WebmasterTD/CastVolumeKnob/esp8266/volume.py

import usocket as socket
import ussl as ssl
import ure as re
import utime as time
import machine
from neopixel import NeoPixel
from ustruct import unpack
import math
import wificonf
import esp
INIT_MSGS = (
            b'\x00\x00\x00Y\x08\x00\x12\x08sender-0\x1a\nreceiver-0"(urn:x-cast:com.google.cast.tp.connection(\x002\x13{"type": "CONNECT"}',
            b'\x00\x00\x00g\x08\x00\x12\x08sender-0\x1a\nreceiver-0"#urn:x-cast:com.google.cast.receiver(\x002&{"type": "GET_STATUS", "requestId": 1}'
            )

VOL_MSGS =  {
            4 : b'\x00\x00\x00\x81\x08\x00\x12\x08sender-0\x1a\nreceiver-0"#urn:x-cast:com.google.cast.receiver(\x002@{"type": "SET_VOLUME", "volume": {"level": ###}, "requestId": $$$}',
            5 : b'\x00\x00\x00\x82\x08\x00\x12\x08sender-0\x1a\nreceiver-0"#urn:x-cast:com.google.cast.receiver(\x002A{"type": "SET_VOLUME", "volume": {"level": ###}, "requestId": $$$}',
            6 : b'\x00\x00\x00\x83\x08\x00\x12\x08sender-0\x1a\nreceiver-0"#urn:x-cast:com.google.cast.receiver(\x002B{"type": "SET_VOLUME", "volume": {"level": ###}, "requestId": $$$}',
            7 : b'\x00\x00\x00\x84\x08\x00\x12\x08sender-0\x1a\nreceiver-0"#urn:x-cast:com.google.cast.receiver(\x002C{"type": "SET_VOLUME", "volume": {"level": ###}, "requestId": $$$}',
            8 : b'\x00\x00\x00\x85\x08\x00\x12\x08sender-0\x1a\nreceiver-0"#urn:x-cast:com.google.cast.receiver(\x002D{"type": "SET_VOLUME", "volume": {"level": ###}, "requestId": $$$}'
            }

STOP_MSGS = {
            1 : b'\x00\x00\x00\x96\x08\x00\x12\x08sender-0\x1a\nreceiver-0"#urn:x-cast:com.google.cast.receiver(\x002U{"type": "STOP", "requestId": $$$, "sessionId": "###"}',
            2 : b'\x00\x00\x00\x97\x08\x00\x12\x08sender-0\x1a\nreceiver-0"#urn:x-cast:com.google.cast.receiver(\x002V{"type": "STOP", "requestId": $$$, "sessionId": "###"}',
            3 : b'\x00\x00\x00\x98\x08\x00\x12\x08sender-0\x1a\nreceiver-0"#urn:x-cast:com.google.cast.receiver(\x002W{"type": "STOP", "requestId": $$$, "sessionId": "###"}'
            }

GAMMA8 =    (  
            0,  0,  0,  0,  0,  0,  0,  0,  0,  0,  0,  0,  0,  0,  0,  0,
            0,  0,  0,  0,  0,  0,  0,  0,  0,  0,  0,  0,  1,  1,  1,  1,
            1,  1,  1,  1,  1,  1,  1,  1,  1,  2,  2,  2,  2,  2,  2,  2,
            2,  3,  3,  3,  3,  3,  3,  3,  4,  4,  4,  4,  4,  5,  5,  5,
            5,  6,  6,  6,  6,  7,  7,  7,  7,  8,  8,  8,  9,  9,  9, 10,
            10, 10, 11, 11, 11, 12, 12, 13, 13, 13, 14, 14, 15, 15, 16, 16,
            17, 17, 18, 18, 19, 19, 20, 20, 21, 21, 22, 22, 23, 24, 24, 25,
            25, 26, 27, 27, 28, 29, 29, 30, 31, 32, 32, 33, 34, 35, 35, 36,
            37, 38, 39, 39, 40, 41, 42, 43, 44, 45, 46, 47, 48, 49, 50, 50,
            51, 52, 54, 55, 56, 57, 58, 59, 60, 61, 62, 63, 64, 66, 67, 68,
            69, 70, 72, 73, 74, 75, 77, 78, 79, 81, 82, 83, 85, 86, 87, 89,
            90, 92, 93, 95, 96, 98, 99,101,102,104,105,107,109,110,112,114,
            115,117,119,120,122,124,126,127,129,131,133,135,137,138,140,142,
            144,146,148,150,152,154,156,158,160,162,164,167,169,171,173,175,
            177,180,182,184,186,189,191,193,196,198,200,203,205,208,210,213,
            215,218,220,223,225,228,231,233,236,239,241,244,247,249,252,255
            )


class Chromecast(object):        
    
    def __init__(self, ip):
        self.ip = ip
        self.request = 2
        self.s = socket.socket(socket.AF_INET, socket.SOCK_STREAM)
        self.s.connect((self.ip, 8009))
        self.s = ssl.wrap_socket(self.s)
        for msg in INIT_MSGS:
            self.s.write(msg)
        self.read_message()
       
    @property
    def get_volume(self):
        return self.vol


    def set_volume(self, volume):
        volume = str(volume/100)
        msg_len = len(volume) + len(str(self.request))
        r_volmsg = VOL_MSGS[msg_len]
        r_volmsg = r_volmsg.replace(b'###', bytes(volume, 'utf-8'))
        r_volmsg = r_volmsg.replace(b'$$$', bytes(str(self.request), 'utf-8'))
        self.s.write(r_volmsg)
        self.request += 1
        self.read_message()

    def disconnect(self):
        self.s.close()
    
    def read_message(self):
        siz = unpack('>I',self.s.read(4))[0]
        status = str(self.s.read(siz))
        self.vol = float(re.search('\"level\":([0-9]\.?[0-9]*)', status).group(1))
        self.vol = int(round(self.vol*100))
        self.sess_id = re.search('\"sessionId\":\"(....................................)', status)
        if self.sess_id:
            self.sess_id = self.sess_id.group(1)
        
    
    def stop_playback(self):
        if self.sess_id:
            msg_size = len(str(self.request))
            stop_msg = STOP_MSGS[msg_size]
            stop_msg = stop_msg.replace(b'###', bytes(self.sess_id, 'utf-8'))
            stop_msg = stop_msg.replace(b'$$$', bytes(str(self.request), 'utf-8'))
            #print(stop_msg)
            self.s.write(stop_msg)
            self.request += 1
            self.read_message()

class NeoPixelRing(NeoPixel):
    
    def __init__(self, led_v_pin, device, *args, **kwargs):
        self.led_v = machine.Pin(led_v_pin, machine.Pin.OUT)
        self.colors = wificonf.DEVICE_COLORS
        self.lightness = wificonf.LED_LIGHTNESS
        self.device = device
        self.turn_on()
        super(NeoPixelRing, self).__init__(*args, **kwargs)

    def change_device(self, device, volume):
        vol = int(volume)
        self.device = device
        rev = list(enumerate(self.vol2pix(vol), 1))
        h, s, v = self.colors[self.device]
        for i in range(16):
            self[i] = self.hsv2rgb(h, s, v)
            self.write()
            time.sleep_ms(30)

        time.sleep_ms(100)
        
        for i, c in rev[::-1]:
            h, s, v = c
            self[i] = self.hsv2rgb(h, s, v)
            self.write()
            time.sleep_ms(30)
        

        self.set_vol(volume)

    def set_vol(self, volume):
        vol = int(volume)
        h, s, v = self.colors[self.device]
        self[0] = self.hsv2rgb(h, s, v)
        for i, color in enumerate(self.vol2pix(vol), 1):
            h, s, v = color
            self[i] = self.hsv2rgb(h, s, v)
        self.write()

    def vol2pix(self, volume):
        pixels = wificonf.neopixel_percents
        hues =   wificonf.neopixel_hues
        for h, p in zip(hues, pixels):
            if (volume/p) > 1:
                yield (h, 1, 1)
            elif (volume/p) > 0:
                yield (h, 1, volume/p)
            else:
                yield (h, 1, 0)
            volume = volume - p
        return

    def error(self):
        for _ in range(3):
            self.fill(self.hsv2rgb(30, 1, 1))
            self.write()
            time.sleep_ms(150)
            self.fill((0, 0, 0))
            self.write()
            time.sleep_ms(100)

    def stop(self):
        self.fill(self.hsv2rgb(0, 1, 1))
        self.write()

    def turn_off(self):
        self.fill((0, 0, 0))
        self.write()
        self.led_v.off()

    def turn_on(self):
        self.led_v.on()

    def hsv2rgb(self, h, s, v):
        h = float(h)
        s = float(s)
        v = float(v) * self.lightness
        h60 = h / 60.0
        h60f = math.floor(h60)
        hi = int(h60f) % 6
        f = h60 - h60f
        p = v * (1 - s)
        q = v * (1 - f * s)
        t = v * (1 - (1 - f) * s)
        r, g, b = 0, 0, 0
        if hi == 0: r, g, b = v, t, p
        elif hi == 1: r, g, b = q, v, p
        elif hi == 2: r, g, b = p, v, t
        elif hi == 3: r, g, b = p, q, v
        elif hi == 4: r, g, b = t, p, v
        elif hi == 5: r, g, b = v, p, q
        r, g, b = int(r * 255), int(g * 255), int(b * 255)
        return GAMMA8[r], GAMMA8[g], GAMMA8[b]
