WebmasterTD/CastVolumeKnob/esp8266/wificonf_example.py

WIFI_SSID = 'YOUR WIFI SSID'
WIFI_PASSWORD = 'YOUR WIFI PASSWORD'
#               IP address,         netmask,        gateway,        DNS
WIFI_CONFIG = ('192.168.0.150', '255.255.255.0', '192.168.0.1', '192.168.0.1')

#set chomecasts ips and names here in your network
CHROMECASTS  = {'192.168.0.164':'LG SH6', '192.168.0.165':'Chromecast audio'}

LED_LIGHTNESS = 0.7

DEVICE_COLORS = {'192.168.0.165':(60,1,1), '192.168.0.164':(300,1,1)}

neopixel_percents = (4.5, 4.5, 2, 2, 2, 2, 2, 2, 2, 2, 2, 2, 2, 34.5, 34.5)

neopixel_hues = (240,210,180,168,156,144,132,120,108,96,84,72,60,30,0)
